furrtek/FBL12SponsorBadge/fw/BadgeFBL12-01/Core/Src/luts.c

// FBL 12 sponsor badge V1
// For STM32F072CBT6
// furrtek 2024

#include "main.h"
#include "luts.h"

const uint8_t sin_lut[256] = {
	128, 131, 134, 137, 140, 143, 146, 149,
	152, 156, 159, 162, 165, 168, 171, 174,
	176, 179, 182, 185, 188, 191, 193, 196,
	199, 201, 204, 206, 209, 211, 213, 216,
	218, 220, 222, 224, 226, 228, 230, 232,
	234, 235, 237, 239, 240, 242, 243, 244,
	246, 247, 248, 249, 250, 251, 251, 252,
	253, 253, 254, 254, 254, 255, 255, 255,
	255, 255, 255, 255, 254, 254, 253, 253,
	252, 252, 251, 250, 249, 248, 247, 246,
	245, 244, 242, 241, 239, 238, 236, 235,
	233, 231, 229, 227, 225, 223, 221, 219,
	217, 215, 212, 210, 207, 205, 202, 200,
	197, 195, 192, 189, 186, 184, 181, 178,
	175, 172, 169, 166, 163, 160, 157, 154,
	151, 148, 145, 142, 138, 135, 132, 129,
	126, 123, 120, 117, 113, 110, 107, 104,
	101, 98, 95, 92, 89, 86, 83, 80,
	77, 74, 71, 69, 66, 63, 60, 58,
	55, 53, 50, 48, 45, 43, 40, 38,
	36, 34, 32, 30, 28, 26, 24, 22,
	20, 19, 17, 16, 14, 13, 11, 10,
	9, 8, 7, 6, 5, 4, 3, 3,
	2, 2, 1, 1, 0, 0, 0, 0,
	0, 0, 0, 1, 1, 1, 2, 2,
	3, 4, 4, 5, 6, 7, 8, 9,
	11, 12, 13, 15, 16, 18, 20, 21,
	23, 25, 27, 29, 31, 33, 35, 37,
	39, 42, 44, 46, 49, 51, 54, 56,
	59, 62, 64, 67, 70, 73, 76, 79,
	81, 84, 87, 90, 93, 96, 99, 103,
	106, 109, 112, 115, 118, 121, 124
};

// For 8kHz samplerate
const uint8_t lpf_lut[256] = {
	112,	// 996Hz
	112,	// 992Hz
	111,	// 989Hz
	111,	// 985Hz
	111,	// 982Hz
	111,	// 978Hz
	111,	// 975Hz
	110,	// 971Hz
	110,	// 968Hz
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
// TOUCH3 3
// TOUCH9 4
// TOUCH8 5
// TOUCH2 6
// TOUCH7 7
// TOUCH1 8
// TOUCH6 9
// TOUCH0 10
// TOUCH5 11

const uint16_t key_lut[16] = {
	(1 << 10),
	(1 << 8),
	(1 << 6),
	(1 << 3),
	(1 << 1),
	(1 << 11),
	(1 << 9),
	(1 << 7),
	(1 << 5),
	(1 << 4),
	(1 << 2),
	(1 << 0),
	0, 0, 0, 0
};

const char key_name_lut[12][3] = {
	"C ",
	"C'",
	"D ",
	"D'",
	"E ",
	"F ",
	"F'",
	"G ",
	"G'",
	"A ",
	"A'",
	"B ",
};

// Octaves 2, 3, 4 - Based on 8000Hz samplerate and 16bit accumulator
// 1Hz: 8.192
const uint16_t tone_lut[(3 * 12) + 1] = {
	535, 567, 601, 637, 675, 715, 757, 802, 850, 901, 954, 1011,
	1071, 1135, 1202, 1274, 1350, 1430, 1515, 1605, 1701, 1802, 1909, 2022,
	2143, 2270, 2405, 2548, 2700, 2860, 3030, 3211, 3402, 3604, 3818, 4045,
	0	// Used for beep silence
};
