furrtek/FBL12SponsorBadge/fw/BadgeFBL12-01/Core/Inc/rec.h

// FBL 12 sponsor badge V1
// For STM32F072CBT6
// furrtek 2024

#ifndef INC_REC_H_
#define INC_REC_H_

void enter_rec_sel();
void handle_rec_sel();
void enter_rec_predef();
void handle_rec_predef();
void enter_rec_active();
void handle_rec_active();
void enter_rec_pitch();
void handle_rec_pitch();

#endif /* INC_REC_H_ */
