furrtek/FBL12SponsorBadge/fw/BadgeFBL12-01/Core/Inc/touch.h

// FBL 12 sponsor badge V1
// For STM32F072CBT6
// furrtek 2024

#ifndef INC_TOUCH_H_
#define INC_TOUCH_H_
#define TOUCH_A_REC ((0 << 2) + 0)
#define TOUCH_OK_PLAY ((0 << 2) + 1)
#define TOUCH_LEAR ((1 << 2) + 0)
#define TOUCH_NOSE ((1 << 2) + 1)
#define TOUCH_REAR ((2 << 2) + 0)

extern volatile uint16_t touch_val[12];
extern const uint16_t touch_thr[12];
extern uint8_t touched[12];
extern uint8_t touched_prev[12];
extern uint8_t touched_rise[12];

uint16_t ReadExtTouch();

#endif /* INC_TOUCH_H_ */
